FormicRobotics/Chronos/hardware/Chronos.PcbDoc.htm

Reporting Options

# File in Newer Format

Date | : | 15.02.2026
Time | : | 18:00:02
Filename | : | D:\github_projects\hw-works\hw-works-main\Chronos\Chronos.PcbDoc

Version | Warning
Release 23.6 | CAUTION - The PCB document contains Footprint parameters. These will be lost when opening the document in a version of Altium Designer that does not support this functionality.

This file was generated by a later version of the software
