FormicRobotics/Chronos/hardware/Chronos_System_Requirements_Document.docx

# SYSTEM REQUIREMENTS DOCUMENT

Project Chronos

Multi-Camera MIPI Synchronization System

for NVIDIA Jetson Orin NX Platform

Prepared By: Umit Kayacik

Document Version: 1.0

Date: December 29, 2025

# 1. Executive Summary

This document defines the complete system requirements for the Chronos project - a custom hardware and software solution designed to synchronize four OV9281 MIPI cameras and aggregate their image streams into a single 2-lane MIPI CSI-2 output for delivery to an NVIDIA Jetson Orin NX platform. The system utilizes a Lattice CrossLink-NX FPGA for camera stream aggregation via virtual channels, enabling all four synchronized cameras to share a single CSI port. Hardware-triggered synchronization ensures sub-microsecond accuracy, with zero-copy transfer of synchronized frames directly into GPU memory for computer vision processing.

# 2. Project Objectives

1. Design and fabricate a custom PCB to interface 4x OV9281 MIPI cameras
1. Implement hardware-level synchronization via trigger signals
2. Aggregate 4 camera streams into single 2-lane MIPI output using Lattice CrossLink-NX FPGA
3. Develop kernel-level driver for zero-copy GPU memory transfer
4. Integrate IMU (ICM-42688-P) with synchronized trigger signal
5. Publish synchronized images using NVIDIA NITROS node
6. Publish IMU data using ROS2 node with FPGA timestamps
7. Design for commercial-grade components to optimize cost for mass production

# 3. System Constraints

## 3.1 Interface Constraints

- Available Jetson Interface: Single 2-lane MIPI CSI-2 port (other ports occupied by existing sensors)
- Solution: Lattice CrossLink-NX FPGA for 4-to-1 MIPI virtual channel aggregation (MANDATORY)
- Total Camera Requirement: 7 cameras total (4 synchronized OV9281 + 3 TBD higher-res cameras)
- Available MIPI Ports: 4x 2-lane ports on Jetson Orin NX (1 for aggregated cameras, 3 for other sensors)

## 3.2 Environmental Constraints

- Component Grade: Commercial temperature range (-10°C to +55°C)
- No Extreme Conditions: No operation below -20°C required (Jetson limitation)
- Commercial Application: Cost-optimized components acceptable

## 3.3 Physical Constraints

- Camera-to-Board Distance: 10-15cm (within MIPI direct connection range of 30cm)
- No Serializer Required: FPD-Link or GMSL not needed for this application

# 4. Hardware Requirements

## 4.1 Camera Module Specifications

Parameter | Specification
Camera Model | SF-C1014OV-B&W-H80
Sensor | OmniVision OV9281 (Global Shutter)
Resolution | 1MP (1280 x 800)
Pixel Size | 3.0 μm × 3.0 μm
Sensor Size | 1/4 inch
Interface | MIPI CSI-2 (2-lane per camera)
Connector | AXT624124 (24-pin FPC)
Frame Rate (Full Res) | Up to 120 fps
Frame Sync | FSIN (Frame Sync Input) - Pin 16
Focal Length | 2.2mm
F-Number | F2.0
FOV (Horizontal) | 80°
TV Distortion | < -1%
Focusing Range | 60cm to infinity
Quantity | 4 units
Cable Length | 10-15cm (MIPI direct connection)

## 4.2 FPGA Requirements (Lattice CrossLink-NX)

Parameter | Specification
Device | Lattice CrossLink-NX (LIFCL-40 or LIFCL-17)
Technology | 28nm FD-SOI (Nexus platform)
MIPI D-PHY | Hardened D-PHY IP, 2.5 Gbps/lane, max 10 Gbps aggregate
Input Configuration | 4x CSI-2 RX interfaces (2-lane each)
Output Configuration | 1x CSI-2 TX interface (2-lane) to Jetson
Virtual Channel Mapping | Camera 1→VC0, Camera 2→VC1, Camera 3→VC2, Camera 4→VC3
Reference Design | 4-to-1 Image Aggregation with CrossLink-NX
Development Tool | Lattice Radiant Software

## 4.3 IMU Requirements

Parameter | Specification
IMU Model | ICM-42688-P
Type | 6-axis MEMS (3-axis gyro + 3-axis accelerometer)
Package | 2.5mm x 3mm x 0.91mm 14-pin LGA
Interface | SPI (up to 24 MHz) / I2C (up to 1 MHz)
Gyroscope Range | ±15.625 to ±2000 dps (programmable)
Accelerometer Range | ±2g, ±4g, ±8g, ±16g (programmable)
FIFO | 2KB buffer
Sync Method | FPGA trigger pulse routed to interrupt pin
Features | External clock input (31-50kHz), programmable interrupts

## 4.4 Carrier Board (Helios by Aerium)

Parameter | Specification
Board Model | Aerium Helios
Dimensions | 59mm x 89.5mm
Weight | 40g (without Jetson module)
Input Voltage | 12-48V DC
Compatible Modules | Jetson Orin NX, Orin Nano, Xavier NX, TX2 NX, Nano
Camera Interface | Quad MIPI camera interface
Features | SuperMode support, Hardware TPM, expanded USB 3.0
PCIe Interface | Available (currently used for NVMe SSD)

## 4.5 Synchronization Requirements

### 4.5.1 Trigger Circuit Specifications

- Trigger Source: FPGA-generated precision timing signal (CrossLink-NX internal PLL)
- Distribution: Low-skew buffer for simultaneous trigger to all 4 cameras and IMU
- Camera Interface: OV9281 FSIN (Frame Sync Input) for external trigger mode
- Trigger Pulse Width: Minimum 2μs (as per OV9281 specification)
- Trigger Voltage Level: 3.3V
- Skew Specification: <100ns between all trigger outputs
- Frame Rate: Configurable up to 120fps
- 5th Camera Sync: Additional sync signal output for external camera (without aggregation)

### 4.5.2 Timestamp Requirements

- Timestamp Source: FPGA-based hardware timer
- Resolution: Microsecond precision
- Synchronization: Identical timestamp applied to all triggered devices (cameras + IMU)

## 4.6 PCB Design Requirements

- Design Tool: Altium Designer
- MIPI Routing: 100Ω differential impedance with tight length matching (±0.1mm within pairs)
- Lane Configuration: Each camera uses 2 data lanes + 1 clock lane (D0±, D1±, CLK±)
- Data Rate: Up to 800 Mbps/lane per camera input
- ESD Protection: Low-capacitance TVS diodes (<0.5pF) on all MIPI lines
- Connectors: Commercial-grade 15-pin FPC connectors

## 4.7 Power Management Requirements

- Camera Power: 1.8V/2.8V/1.2V rails (~150mW per camera)
- FPGA Power: 1.0V core, 1.8V I/O, 2.5V PLL
- Total Power Budget: ~2.5W for entire board

# 5. Software Requirements

## 5.1 FPGA Firmware Requirements

1. CSI-2 RX Controllers: 4x receivers with packet parsing and VC extraction
1. Frame Buffer: Internal SRAM for line buffering during aggregation
2. CSI-2 TX Controller: Packet reconstruction with VC tagging
3. Trigger Generator: Precision timing with configurable frame rate
4. Timestamp Counter: Hardware timer for synchronized timestamps
5. I2C Master: Camera sensor configuration interface

## 5.2 Linux Driver Requirements

### 5.2.1 Kernel Driver Architecture

- V4L2 Subdevice Driver: OV9281 sensor control (exposure, gain, trigger mode)
- NVCSI Integration: Interface with NVIDIA camera subsystem
- VC Demultiplexing: Separate VC0-VC3 streams into /dev/video0-3
- Device Tree: Custom DTS overlay for Orin NX

### 5.2.2 Zero-Copy GPU Memory Transfer

- NvBuffer API: DMA-capable memory allocation
- CUDA-EGL Interop: Direct mapping to CUDA memory without CPU copy
- Buffer Queue: Triple-buffering to prevent frame drops

## 5.3 ROS2 Integration Requirements

### 5.3.1 Camera Node (NITROS)

- Framework: NVIDIA Isaac ROS NITROS
- Zero-Copy Support: Type adaptation and type negotiation for GPU memory sharing
- Message Type: isaac_ros_nitros_image_type
- Topics: 4 synchronized image streams with FPGA timestamps
- Performance: Full resolution (1280x800) at 60fps minimum

### 5.3.2 IMU Node

- Framework: Standard ROS2 node
- Message Type: sensor_msgs/Imu
- Interface: SPI communication with ICM-42688-P
- Timestamp: FPGA timestamps included in message header
- FSYNC Flag: Trigger event marker in IMU data stream

# 6. Performance Requirements

Requirement | Specification
Image Resolution | 1280 x 800 (1MP)
Target Frame Rate | 60 fps (synchronized)
Maximum Frame Rate | 120 fps (OV9281 capability)
Synchronization Accuracy | < 100ns skew between cameras
Timestamp Resolution | Microsecond precision
Memory Transfer | Zero-copy to GPU memory
Latency (Glass-to-GPU) | Minimize - no display output
IMU Sample Rate | Synchronized with camera trigger

# 7. Deliverables

## 7.1 Hardware Deliverables

1. Complete schematic design files (Altium Designer)
1. PCB layout files with Gerber outputs
2. Bill of Materials (BOM)
3. 3x Working prototype boards (assembled and tested)

## 7.2 Software Deliverables

1. FPGA firmware source code (Lattice Radiant project)
1. Kernel driver source code
2. ROS2 NITROS camera node for synchronized images
3. ROS2 IMU node with FSYNC support
4. Sample application demonstrating zero-copy GPU memory access
5. Technical documentation package

## 7.3 Demonstration Requirements

- Demo 1: Zero-copy transfer of synced images at full resolution (1280x800) and 60fps mapped to GPU memory
- Demo 2: IMU stream readout on Jetson including FPGA timestamps
- Demo 3: FSYNC flag indication when trigger signal rises

# 8. Reference Links

- Aerium Helios Carrier Board: https://aerium.co.il/products/helios
- Helios Documentation: https://docs.aerium.co.il/Product%20Manuals/Helios/
- Lattice CrossLink-NX: https://www.latticesemi.com/Products/FPGAandCPLD/CrossLink-NX
- 4-to-1 Image Aggregation Reference Design: https://www.latticesemi.com/products/designsoftwareandip/intellectualproperty/referencedesigns/referencedesign04/4to1
- NVIDIA Isaac ROS NITROS: https://nvidia-isaac-ros.github.io/concepts/nitros/index.html
- OV9281 Sensor: https://www.ovt.com/products/ov9281/
- ICM-42688-P IMU: https://invensense.tdk.com/products/motion-tracking/6-axis/icm-42688-p/

# 9. Document History

Version | Date | Author | Changes
1.0 | Dec 29, 2025 | Umit Kayacik | Initial Release

Chronos Project - System Requirements Document
